oribotic/oribotic-instruments/oribotic-instrument-atmega32u4/src/MPR121/MPR121.cpp

/*******************************************************************************

 Bare Conductive MPR121 library
 ------------------------------

 MPR121.cpp - MPR121 class implementation file

 Based on code by Jim Lindblom and plenty of inspiration from the Freescale
 Semiconductor datasheets and application notes.

 Bare Conductive code written by Stefan Dzisiewski-Smith, Peter Krige
 and Szymon Kaliski.

 This work is licensed under a MIT license https://opensource.org/licenses/MIT

 Copyright (c) 2016, Bare Conductive

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
*******************************************************************************/

extern "C" {
  #include <stdlib.h>
  #include <string.h>
  #include <inttypes.h>
}

#include "MPR121.h"
#include <Arduino.h>

#ifdef ARDUINO_ARCH_AVR
  #include <EEPROM.h>
#endif

#define NOT_INITED_BIT 0
#define ADDRESS_UNKNOWN_BIT 1
#define READBACK_FAIL_BIT 2
#define OVERCURRENT_FLAG_BIT 3
#define OUT_OF_RANGE_BIT 4

MPR121_t::MPR121_t(){
  address = 0x5C;    // default address is 0x5C, for use with Bare Conductive Touch Board
  ECR_backup = 0x00;
  running = false;
  error = 1<<NOT_INITED_BIT; // initially, we're not initialised
  touchData = 0;
  lastTouchData = 0;
  autoTouchStatusFlag = false;
}

void MPR121_t::setRegister(uint8_t reg, uint8_t value){

  bool wasRunning = false;;

  if(reg==MPR121_ECR){  // if we are modding MPR121_ECR, update our internal running status
    if(value&0x3F){
      running = true;
    } else {
      running = false;
    }
  } else if(reg<MPR121_CTL0){
    wasRunning = running;
    if(wasRunning) stop();  // we should ALWAYS be in stop mode for this
                // unless modding MPR121_ECR or GPIO / LED register
  }

    Wire.beginTransmission(address);
    Wire.write(reg);
    Wire.write(value);
    if(Wire.endTransmission()!=0){
      error |= 1<<ADDRESS_UNKNOWN_BIT; // set address unknown bit
    } else {
      error &= ~(1<<ADDRESS_UNKNOWN_BIT);
    }

    if(wasRunning) run();   // restore run mode if necessary
}

uint8_t MPR121_t::getRegister(uint8_t reg){
  uint8_t scratch;

    Wire.beginTransmission(address);
    Wire.write(reg); // set address to read from our requested register
    Wire.endTransmission(false); // repeated start

    if(Wire.requestFrom(address,(uint8_t)1) == 1){  // just a single byte
      error &= ~(1<<ADDRESS_UNKNOWN_BIT); // all good, clear the bit
      scratch = Wire.read();
    } else {
      error |= 1<<ADDRESS_UNKNOWN_BIT; //set the bit - something went wrong
    }

    // auto update errors for registers with error data
    if(reg == MPR121_TS2 && ((scratch&0x80)!=0)){
      error |= 1<<OVERCURRENT_FLAG_BIT;
    } else {
      error &= ~(1<<OVERCURRENT_FLAG_BIT);
    }
    if((reg == MPR121_OORS1 || reg == MPR121_OORS2) && (scratch!=0)){
      error |= 1<<OUT_OF_RANGE_BIT;
    } else {
      error &= ~(1<<OUT_OF_RANGE_BIT);
    }
    return scratch;
}

bool MPR121_t::begin(uint8_t address, uint8_t touchThreshold, uint8_t releaseThreshold, uint8_t interruptPin){

  // SDA and SCL should idle high, but MPR121 can get stuck waiting to complete a transaction
  // this code detects this state and releases us from it

  boolean stuck_transaction = false;
  uint8_t stuck_transaction_retry_count = 0;
  const uint8_t stuck_transaction_retry_MAX = 10;

  ::pinMode( PIN_WIRE_SDA, INPUT_PULLUP );
  ::pinMode( PIN_WIRE_SCL, INPUT_PULLUP );

  do{
    if(( ::digitalRead( PIN_WIRE_SDA ) == LOW ) && ( ::digitalRead( PIN_WIRE_SCL ) == HIGH )){
      stuck_transaction = true;
      ::pinMode( PIN_WIRE_SCL, OUTPUT );
      ::digitalWrite( PIN_WIRE_SCL, LOW );
      delay( 1 ); // this is way longer than required (would be 1.25us at 400kHz) but err on side of caution
      ::pinMode( PIN_WIRE_SCL, INPUT_PULLUP );
      stuck_transaction_retry_count++;
    } else {
      stuck_transaction = false;
    }
  } while ( stuck_transaction && ( stuck_transaction_retry_count < stuck_transaction_retry_MAX ));

  // TODO: add new error code that can be handled externally
  if( stuck_transaction_retry_count > 0){
    if( stuck_transaction ){
    } else {
    }
  }

  // now we've released (if necessary) we can get on with things
  Wire.begin();

  // addresses only valid 0x5A to 0x5D - if we don't change the address it stays at default
  if(address>=0x5A && address<=0x5D)
  {
    this->address = address; // need to be specific here
  }

  error &= ~(1<<NOT_INITED_BIT); // clear NOT_INITED error flag

  if( reset() ){
    // default values...
    applySettings( &defaultSettings );

    // only apply thresholds if they differ from existing defaults
    if( touchThreshold != defaultSettings.TTHRESH ){
      setTouchThreshold( touchThreshold );
    }

    if( releaseThreshold != defaultSettings.RTHRESH ){
      setReleaseThreshold( releaseThreshold );
    }

    if( interruptPin != defaultSettings.INTERRUPT ){
      setInterruptPin( interruptPin );
    }

    return true;

  } else {
    return false;
  }
}

void MPR121_t::clearSavedThresholds() {
  #ifdef ARDUINO_ARCH_AVR
    uint8_t maxElectrodes = 12;
    int len = E2END;

    for(uint8_t i=0; i<13; i++){
      EEPROM.write(len - (i + 1), 255);
      EEPROM.write(len - (i + 1) - maxElectrodes, 255);
    }
  #endif
}

void MPR121_t::restoreSavedThresholds() {
  #ifdef ARDUINO_ARCH_AVR
    uint8_t maxElectrodes = 12;
    int len = E2END;

    for(uint8_t i=0; i<13; i++){
      uint8_t releaseThreshold = EEPROM.read(len - (i + 1));
      uint8_t touchThreshold = EEPROM.read(len - (i + 1) - maxElectrodes);

      if (touchThreshold < 255) {
        setTouchThreshold(i, touchThreshold + 1); // EEPROM values are saved off-by-one
      }
      else {
        setTouchThreshold(i, defaultSettings.TTHRESH);
      }

      if (releaseThreshold < 255) {
        setReleaseThreshold(i, releaseThreshold + 1); // EEPROM values are saved off-by-one
      }
      else {
        setReleaseThreshold(i, defaultSettings.RTHRESH);
      }
    }
  #endif
}

void MPR121_t::goSlow(){
  Wire.setClock(100000L); // set I2C clock to 100kHz
}

void MPR121_t::goFast(){
    Wire.setClock(400000L); // set I2C clock to 400kHz
}

void MPR121_t::run(){
  if(!isInited()) return;
  setRegister(MPR121_ECR, ECR_backup); // restore backup to return to run mode
}

void MPR121_t::stop(){
  if(!isInited()) return;
  ECR_backup = getRegister(MPR121_ECR); // backup MPR121_ECR to restore when we enter run
  setRegister(MPR121_ECR, ECR_backup & 0xC0); // turn off all electrodes to stop
}

bool MPR121_t::reset(){
  // return true if we successfully reset a device at the
  // address we are expecting

  // MPR121_AFE2 is one of the few registers that defaults to a non-zero value -
  // checking it is sensible as reading back an incorrect value implies
  // something went wrong - we also check MPR121_TS2 bit 7 to see if we have an
  // overcurrent flag set

  setRegister(MPR121_SRST, 0x63); // soft reset

  if(getRegister(MPR121_AFE2)!=0x24){
    error |= 1<<READBACK_FAIL_BIT;
  } else {
    error &= ~(1<<READBACK_FAIL_BIT);
  }

  if((getRegister(MPR121_TS2)&0x80)!=0){
    error |= 1<<OVERCURRENT_FLAG_BIT;
  } else {
    error &= ~(1<<OVERCURRENT_FLAG_BIT);
  }

  if(getError()==NOT_INITED || getError()==NO_ERROR){ // if our only error is that we are not inited...
    return true;
  } else {
    return false;
  }
}

void MPR121_t::applySettings(MPR121_settings_t *settings){
  bool wasRunning = running;
  if(wasRunning) stop();  // can't change most regs when running - checking
              // here avoids multiple stop() / run() calls

  setRegister(MPR121_MHDR,settings->MHDR);
  setRegister(MPR121_NHDR,settings->NHDR);
  setRegister(MPR121_NCLR,settings->NCLR);
  setRegister(MPR121_FDLR,settings->FDLR);
  setRegister(MPR121_MHDF,settings->MHDF);
  setRegister(MPR121_NHDF,settings->NHDF);
  setRegister(MPR121_NCLF,settings->NCLF);
  setRegister(MPR121_FDLF,settings->FDLF);
  setRegister(MPR121_NHDT,settings->NHDT);
  setRegister(MPR121_NCLT,settings->NCLT);
  setRegister(MPR121_FDLT,settings->FDLT);
  setRegister(MPR121_MHDPROXR,settings->MHDPROXR);
  setRegister(MPR121_NHDPROXR,settings->NHDPROXR);
  setRegister(MPR121_NCLPROXR,settings->NCLPROXR);
  setRegister(MPR121_FDLPROXR,settings->FDLPROXR);
  setRegister(MPR121_MHDPROXF,settings->MHDPROXF);
  setRegister(MPR121_NHDPROXF,settings->NHDPROXF);
  setRegister(MPR121_NCLPROXF,settings->NCLPROXF);
  setRegister(MPR121_FDLPROXF,settings->FDLPROXF);
  setRegister(MPR121_NHDPROXT,settings->NHDPROXT);
  setRegister(MPR121_NCLPROXT,settings->NCLPROXT);
  setRegister(MPR121_FDLPROXT,settings->FDLPROXT);
  setRegister(MPR121_DTR, settings->DTR);
  setRegister(MPR121_AFE1, settings->AFE1);
  setRegister(MPR121_AFE2, settings->AFE2);
  setRegister(MPR121_ACCR0, settings->ACCR0);
  setRegister(MPR121_ACCR1, settings->ACCR1);
  setRegister(MPR121_USL, settings->USL);
  setRegister(MPR121_LSL, settings->LSL);
  setRegister(MPR121_TL, settings->TL);

  setRegister(MPR121_ECR, settings->ECR);

  error &= ~(1<<NOT_INITED_BIT); // clear not inited error as we have just inited!
  setTouchThreshold(settings->TTHRESH);
  setReleaseThreshold(settings->RTHRESH);
  setInterruptPin(settings->INTERRUPT);

  if(wasRunning) run();
}

mpr121_error_t MPR121_t::getError(){

  // important - this resets the IRQ pin - as does any I2C comms

  getRegister(MPR121_OORS1);  // OOR registers - we may not have read them yet,
  getRegister(MPR121_OORS2);  // whereas the other errors should have been caught

  // order of error precedence is determined in this logic block

  if(!isInited()) return NOT_INITED; // this has its own checker function

  if((error & (1<<ADDRESS_UNKNOWN_BIT)) != 0){
    return ADDRESS_UNKNOWN;
  } else if((error & (1<<READBACK_FAIL_BIT)) != 0){
    return READBACK_FAIL;
  } else if((error & (1<<OVERCURRENT_FLAG_BIT)) != 0){
    return OVERCURRENT_FLAG;
  } else if((error & (1<<OUT_OF_RANGE_BIT)) != 0){
    return OUT_OF_RANGE;
  } else return NO_ERROR;

}

void MPR121_t::clearError(){
  error = 0;
}

bool MPR121_t::isRunning(){
  return running;
}

bool MPR121_t::isInited(){
  return (error & (1<<NOT_INITED_BIT)) == 0;
}

void MPR121_t::updateTouchData(){
  if(!isInited()) return;

  autoTouchStatusFlag = false;

  lastTouchData = touchData;
  touchData = (unsigned int)getRegister(MPR121_TS1) + ((unsigned int)getRegister(MPR121_TS2)<<8);
}

bool MPR121_t::getTouchData(uint8_t electrode){
  if(electrode>12 || !isInited()) return false; // avoid out of bounds behaviour

  return((touchData>>electrode)&1);
}

uint8_t MPR121_t::getNumTouches(){
  if(!isInited()) return(0xFF);

  uint8_t scratch = 0;
  for(uint8_t i=0; i<13; i++){
    if(getTouchData(i)) scratch++;
  }

  return(scratch);
}

bool MPR121_t::getLastTouchData(uint8_t electrode){
  if(electrode>12 || !isInited()) return false; // avoid out of bounds behaviour

  return((lastTouchData>>electrode)&1);
}

bool MPR121_t::updateFilteredData(){
  if(!isInited()) return(false);

  uint8_t LSB, MSB;

  Wire.beginTransmission(address);
  Wire.write(MPR121_E0FDL); // set address register to read from the start of the
                //filtered data
  Wire.endTransmission(false); // repeated start

  if(touchStatusChanged()) {
    autoTouchStatusFlag = true;
  }

  if(Wire.requestFrom(address,(uint8_t)26)==26){
    for(int i=0; i<13; i++){ // 13 filtered values
      if(touchStatusChanged()) {
        autoTouchStatusFlag = true;
      }
      LSB = Wire.read();
      if(touchStatusChanged()) {
        autoTouchStatusFlag = true;
      }
      MSB = Wire.read();
      filteredData[i] = ((MSB << 8) | LSB);
    }
    return(true);
  } else {
    // if we don't get back all 26 values we requested, don't update the FDAT values
    // and return false
    return(false);
  }
}

int MPR121_t::getFilteredData(uint8_t electrode){
  if(electrode>12 || !isInited()) return(0xFFFF); // avoid out of bounds behaviour

  return(filteredData[electrode]);
}

bool MPR121_t::updateBaselineData(){
  if(!isInited()) return(false);

  Wire.beginTransmission(address);
  Wire.write(MPR121_E0BV);  // set address register to read from the start of the
                // baseline data
  Wire.endTransmission(false); // repeated start

  if(touchStatusChanged()) {
    autoTouchStatusFlag = true;
  }

  if(Wire.requestFrom(address,(uint8_t)13)==13){
    for(int i=0; i<13; i++){ // 13 filtered values
      if(touchStatusChanged()) {
        autoTouchStatusFlag = true;
      }
      baselineData[i] = Wire.read()<<2;
    }
    return(true);
    } else {
      // if we don't get back all 26 values we requested, don't update the BVAL values
      // and return false
    return(false);
  }
}

int MPR121_t::getBaselineData(uint8_t electrode){
  if(electrode>12 || !isInited()) return(0xFFFF); // avoid out of bounds behaviour

  return(baselineData[electrode]);
}

bool MPR121_t::isNewTouch(uint8_t electrode){
  if(electrode>12 || !isInited()) return(false); // avoid out of bounds behaviour
  return((getLastTouchData(electrode) == false) && (getTouchData(electrode) == true));
}

bool MPR121_t::isNewRelease(uint8_t electrode){
  if(electrode>12 || !isInited()) return(false); // avoid out of bounds behaviour
  return((getLastTouchData(electrode) == true) && (getTouchData(electrode) == false));
}

void MPR121_t::updateAll(){
  updateTouchData();
  updateBaselineData();
  updateFilteredData();
}

void MPR121_t::setTouchThreshold(uint8_t val){
  if(!isInited()) return;
  bool wasRunning = running;

  if(wasRunning) stop();  // can only change thresholds when not running
              // checking here avoids multiple stop() / run()
              // calls

  for(uint8_t i=0; i<13; i++){
    setTouchThreshold(i, val);
  }

  if(wasRunning) run();
}

void MPR121_t::saveTouchThreshold(uint8_t electrode, uint8_t val){
  #ifdef ARDUINO_ARCH_AVR
    if(electrode>12 || !isInited()) return; // avoid out of bounds behaviour

    setTouchThreshold(electrode, val);

    // store to EEPROM
    uint8_t maxElectrodes = 12;
    int len = E2END;
    int addr = len - maxElectrodes - (electrode + 1);
    EEPROM.write(addr, val - 1); // val - 1 so 255 stays as never-written-to
  #endif
}

void MPR121_t::setTouchThreshold(uint8_t electrode, uint8_t val){
  if(electrode>12 || !isInited()) return; // avoid out of bounds behaviour

  // this relies on the internal register map of the MPR121
  setRegister(MPR121_E0TTH + (electrode<<1), val);
}

void MPR121_t::setReleaseThreshold(uint8_t val){
  if(!isInited()) return;
  bool wasRunning = running;

  if(wasRunning) stop();  // can only change thresholds when not running
              // checking here avoids multiple stop / starts

  for(uint8_t i=0; i<13; i++){
    setReleaseThreshold(i,val);
  }

  if(wasRunning) run();
}

void MPR121_t::setReleaseThreshold(uint8_t electrode, uint8_t val){
  if(electrode>12 || !isInited()) return; // avoid out of bounds behaviour

  // this relies on the internal register map of the MPR121
  setRegister(MPR121_E0RTH + (electrode<<1), val);
}

void MPR121_t::saveReleaseThreshold(uint8_t electrode, uint8_t val){
  #ifdef ARDUINO_ARCH_AVR
    if(electrode>12 || !isInited()) return; // avoid out of bounds behaviour

    setReleaseThreshold(electrode, val);

    // store to EEPROM
    int len = E2END;
    int addr = len - (electrode + 1);
    EEPROM.write(addr, val - 1); // val - 1 so 255 stays as never-written-to
  #endif
}

uint8_t MPR121_t::getTouchThreshold(uint8_t electrode){
  if(electrode>12 || !isInited()) return(0xFF); // avoid out of bounds behaviour
  return(getRegister(MPR121_E0TTH+(electrode<<1))); // "255" issue is in here somewhere
  //return(101);
}

uint8_t MPR121_t::getReleaseThreshold(uint8_t electrode){
  if(electrode>12 || !isInited()) return(0xFF); // avoid out of bounds behaviour
  return(getRegister(MPR121_E0RTH+(electrode<<1))); // "255" issue is in here somewhere
  //return(51);
}

void MPR121_t::setInterruptPin(uint8_t pin){
  // :: here forces the compiler to use Arduino's pinMode, not MPR121's
  if(!isInited()) return;
  ::pinMode(pin, INPUT_PULLUP);
  interruptPin = pin;
}

bool MPR121_t::touchStatusChanged(){
  // :: here forces the compiler to use Arduino's digitalRead, not MPR121's
  return(autoTouchStatusFlag || (!::digitalRead(interruptPin)));
}

void MPR121_t::setProxMode(mpr121_proxmode_t mode){

  if(!isInited()) return;

  bool wasRunning = running;

  if(wasRunning) stop();

  switch(mode){
    case PROX_DISABLED:
      ECR_backup &= ~(3<<4);  // ELEPROX_EN[1:0] = 00
      break;
    case PROX_0_1:
      ECR_backup |=  (1<<4);  // ELEPROX_EN[1:0] = 01
      ECR_backup &= ~(1<<5);
      break;
    case PROX_0_3:
      ECR_backup &= ~(1<<4);  // ELEPROX_EN[1:0] = 10
      ECR_backup |=  (1<<5);
      break;
    case PROX_0_11:
      ECR_backup |=  (3<<4);  // ELEPROX_EN[1:0] = 11
      break;
  }

  if(wasRunning) run();
}

void MPR121_t::setCalibrationLock(mpr121_cal_lock_t lock){

  if(!isInited()) return;

  bool wasRunning = running;

  if(wasRunning) stop();

  switch(lock){
    case CAL_LOCK_ENABLED:
      ECR_backup &= ~(3<<6);  // CL[1:0] = 00
      break;
    case CAL_LOCK_DISABLED:
      ECR_backup |=  (1<<6);  // CL[1:0] = 01
      ECR_backup &= ~(1<<7);
      break;
    case CAL_LOCK_ENABLED_5_BIT_COPY:
      ECR_backup &= ~(1<<6);  // CL[1:0] = 10
      ECR_backup |=  (1<<7);
      break;
    case CAL_LOCK_ENABLED_10_BIT_COPY:
      ECR_backup |=  (3<<4);  // CL[1:0] = 11
      break;
  }

  if(wasRunning) run();
}

void MPR121_t::setGlobalCDC(uint8_t CDC){
  if(CDC > 63) return; // current is only valid 0..63uA

  setRegister(MPR121_AFE1, (getRegister(MPR121_AFE1) & 0xC0) | CDC);
}

void MPR121_t::setElectrodeCDC(uint8_t electrode, uint8_t CDC){
  if(CDC > 63 || electrode > 12) return; // current is only valid 0..63uA, electrode only valid 0..12

  setRegister(MPR121_CDC0 + electrode, CDC);
}

void MPR121_t::setGlobalCDT(mpr121_CDT_t CDT){
  setRegister(MPR121_AFE2, (getRegister(MPR121_AFE2) & 0x1F) | (CDT << 5));
}

void MPR121_t::setElectrodeCDT(uint8_t electrode, mpr121_CDT_t CDT){
  setRegister(MPR121_CDT01 + (electrode >> 1), (getRegister(MPR121_CDT01 + (electrode >> 1)) & (0x0F << (((electrode + 1) % 2)<<2))) | (CDT << ((electrode % 2)<<2)));
}

bool MPR121_t::autoSetElectrodeCDC(uint8_t electrode, uint16_t VCC_mV){
  uint16_t upper_limit_FDAT = (uint16_t)((((uint32_t)VCC_mV - 700)*256)/VCC_mV) << 2;
  uint16_t target_FDAT = (uint16_t)(((uint32_t)upper_limit_FDAT * 90) / 100);
  uint16_t lower_limit_FDAT = (uint16_t)(((uint32_t)upper_limit_FDAT * 65) / 100);

  uint16_t this_value;
  int16_t last_distance;
  int16_t this_distance;

  const uint8_t max_num_delay_loops = 100;
  uint8_t num_delay_loops;

  bool scratch = false; // default to failure
  uint8_t saved_num_enabled_electrodes = getNumEnabledElectrodes();

  setNumEnabledElectrodes(electrode + 1); // reducing the number of running electrodes to a minimum speeds things up
  if(!running) run();

  for(uint8_t CDC = 1; CDC < 63; CDC ++){
    setElectrodeCDC(electrode, CDC);
    num_delay_loops = 0;

    do{
      updateFilteredData();
    } while((getFilteredData(electrode) == 0) && (num_delay_loops++ < max_num_delay_loops));

    this_value = getFilteredData(electrode);

    this_distance = (uint16_t)(abs((int16_t)this_value - (int16_t)target_FDAT)); // TODO: tidy up signed / unsigned types here
    if(CDC > 1){ // only need to see if we need to quit once we have at least two measurements to compare
      if(this_distance > last_distance){ // if we got further away from our target this setting should work (slightly prefer higher values)
        setElectrodeCDC(electrode, CDC);
        if((this_value >= lower_limit_FDAT) && (this_value <= upper_limit_FDAT)){
          scratch = true; // success
        }
        break;
      } else if(CDC == 63){ // or if we're at the end of the available adjustment, see if we're close enough
        setElectrodeCDC(electrode, CDC);
        if((this_value >= lower_limit_FDAT) && (this_value <= upper_limit_FDAT)){
          scratch = true; // success
        }
        break;
      }
    }
    last_distance = this_distance;
  }

  setRegister(MPR121_ECR, ECR_backup);
  setNumEnabledElectrodes(saved_num_enabled_electrodes); // have to do this separately as ECR_backup gets invalidated by setNumEnabledElectrodes(electrode + 1);

  return(scratch);
}

bool MPR121_t::autoSetElectrodeCDC(uint8_t electrode){
  // default to 3.3V VCC if not explicitly stated
  return(autoSetElectrodeCDC(electrode, 3300));
}

bool MPR121_t::autoSetElectrodeCDC(){
  bool scratch = true;
  for(uint8_t i=0; i<getNumEnabledElectrodes(); i++){
    scratch = autoSetElectrodeCDC(i) ? scratch : false;
  }

  return(scratch);
}

bool MPR121_t::autoSetElectrodes(uint16_t VCC_mV, bool fixedChargeTime){
  uint8_t USL = (uint8_t)((((uint32_t)VCC_mV - 700)*256)/VCC_mV);
  uint8_t T_L = (uint8_t)(((uint16_t)USL * 90) / 100);
  uint8_t LSL = (uint8_t)(((uint16_t)USL * 65) / 100);
  bool wasRunning = running;

  stop();

  setRegister(MPR121_USL, USL);
  setRegister(MPR121_TL, T_L);
  setRegister(MPR121_LSL, LSL);

  // don't enable retry, copy other settings from elsewhere
  // setRegister(MPR121_ACCR0, 1 | ((ECR_backup & 0xC0) >> 4) | (getRegister(MPR121_AFE1) & 0xC0));
  // enable retry, copy other settings from elsewhere
  setRegister(MPR121_ACCR0, 0x31 | ((ECR_backup & 0xC0) >> 4) | (getRegister(MPR121_AFE1) & 0xC0)); 
  // fixed charge time is useful for designs with higher lead-in resistance - e.g. using Bare Electric Paint
  setRegister(MPR121_ACCR1, fixedChargeTime ? 1 << 7 : 0); 

  if(wasRunning){
    run();
  }

  // wait a bit before reading back the out or range register
  delayMicroseconds(10);

  return(!(getRegister(MPR121_OORS2) & 0xC0));
}

bool MPR121_t::autoSetElectrodes(bool fixedChargeTime){
  return(autoSetElectrodes(3300, fixedChargeTime));
}

void MPR121_t::setNumDigPins(uint8_t numPins){
  if(!isInited()) return;
  bool wasRunning = running;

  if(numPins>8) numPins = 8; // maximum number of GPIO pins is 8 out of 12

  if(wasRunning){
    stop(); // have to stop to change MPR121_ECR
  }
  ECR_backup = (0x0F&(12-numPins)) | (ECR_backup&0xF0);
  if(wasRunning){
    run();
  }
}

void MPR121_t::setNumEnabledElectrodes(uint8_t numElectrodes){
  if(!isInited()) return;
  bool wasRunning = running;

  if(numElectrodes>12) numElectrodes = 12; // avoid out-of-bounds behaviour

  if(wasRunning){
    stop(); // have to stop to change MPR121_ECR
  }
  ECR_backup = (0x0F&numElectrodes) | (ECR_backup&0xF0);
  if(wasRunning){
    run();
  }
}

uint8_t MPR121_t::getNumEnabledElectrodes(){
  if(!isInited()) return(0xFF);

  return(getRegister(MPR121_ECR) & 0x0F);
}

void MPR121_t::pinMode(uint8_t electrode, mpr121_pinf_t mode){

  // only valid for ELE4..ELE11
  if(electrode<4 || electrode >11 || !isInited()) return;

  // LED0..LED7
  uint8_t bitmask = 1<<(electrode-4);

  switch(mode){
    case INPUT_PULLDOWN:
      // MPR121_EN = 1
      // MPR121_DIR = 0
      // MPR121_CTL0 = 1
      // MPR121_CTL1 = 0
      setRegister(MPR121_EN, getRegister(MPR121_EN) | bitmask);
      setRegister(MPR121_DIR, getRegister(MPR121_DIR) & ~bitmask);
      setRegister(MPR121_CTL0, getRegister(MPR121_CTL0) | bitmask);
      setRegister(MPR121_CTL1, getRegister(MPR121_CTL1) & ~bitmask);
      break;

    case OUTPUT_HIGHSIDE:
      // MPR121_EN = 1
      // MPR121_DIR = 1
      // MPR121_CTL0 = 1
      // MPR121_CTL1 = 1
      setRegister(MPR121_EN, getRegister(MPR121_EN) | bitmask);
      setRegister(MPR121_DIR, getRegister(MPR121_DIR) | bitmask);
      setRegister(MPR121_CTL0, getRegister(MPR121_CTL0) | bitmask);
      setRegister(MPR121_CTL1, getRegister(MPR121_CTL1) | bitmask);
      break;

    case OUTPUT_LOWSIDE:
      // MPR121_EN = 1
      // MPR121_DIR = 1
      // MPR121_CTL0 = 1
      // MPR121_CTL1 = 0
      setRegister(MPR121_EN, getRegister(MPR121_EN) | bitmask);
      setRegister(MPR121_DIR, getRegister(MPR121_DIR) | bitmask);
      setRegister(MPR121_CTL0, getRegister(MPR121_CTL0) | bitmask);
      setRegister(MPR121_CTL1, getRegister(MPR121_CTL1) & ~bitmask);
      break;

    default:
      break;
  }
}

void MPR121_t::pinMode(uint8_t electrode, int mode){
  // this is to catch the fact that Arduino prefers its definitions of
  // INPUT, OUTPUT and INPUT_PULLUP to ours...

  // only valid for ELE4..ELE11
  if(electrode<4 || electrode >11 || !isInited()) return;

  uint8_t bitmask = 1<<(electrode-4);

  switch(mode){
    case OUTPUT:
      // MPR121_EN = 1
      // MPR121_DIR = 1
      // MPR121_CTL0 = 0
      // MPR121_CTL1 = 0
      setRegister(MPR121_EN, getRegister(MPR121_EN) | bitmask);
      setRegister(MPR121_DIR, getRegister(MPR121_DIR) | bitmask);
      setRegister(MPR121_CTL0, getRegister(MPR121_CTL0) & ~bitmask);
      setRegister(MPR121_CTL1, getRegister(MPR121_CTL1) & ~bitmask);
      break;

    case INPUT:
      // MPR121_EN = 1
      // MPR121_DIR = 0
      // MPR121_CTL0 = 0
      // MPR121_CTL1 = 0
      setRegister(MPR121_EN, getRegister(MPR121_EN) | bitmask);
      setRegister(MPR121_DIR, getRegister(MPR121_DIR) & ~bitmask);
      setRegister(MPR121_CTL0, getRegister(MPR121_CTL0) & ~bitmask);
      setRegister(MPR121_CTL1, getRegister(MPR121_CTL1) & ~bitmask);
      break;

    case INPUT_PULLUP:
      // MPR121_EN = 1
      // MPR121_DIR = 0
      // MPR121_CTL0 = 1
      // MPR121_CTL1 = 1
      setRegister(MPR121_EN, getRegister(MPR121_EN) | bitmask);
      setRegister(MPR121_DIR, getRegister(MPR121_DIR) & ~bitmask);
      setRegister(MPR121_CTL0, getRegister(MPR121_CTL0) | bitmask);
      setRegister(MPR121_CTL1, getRegister(MPR121_CTL1) | bitmask);
      break;

    default:
      break;
  }
}

void MPR121_t::digitalWrite(uint8_t electrode, uint8_t val){

  // avoid out of bounds behaviour

  if(electrode<4 || electrode>11 || !isInited()) return;

  if(val){
    setRegister(MPR121_SET, 1<<(electrode-4));
  } else {
    setRegister(MPR121_CLR, 1<<(electrode-4));
  }
}

void MPR121_t::digitalToggle(uint8_t electrode){

  // avoid out of bounds behaviour

  if(electrode<4 || electrode>11 || !isInited()) return;

  setRegister(MPR121_TOG, 1<<(electrode-4));
}

bool MPR121_t::digitalRead(uint8_t electrode){

  // avoid out of bounds behaviour

  if(electrode<4 || electrode>11 || !isInited()) return false;

  return(((getRegister(MPR121_DAT)>>(electrode-4))&1)==1);
}

void MPR121_t::analogWrite(uint8_t electrode, uint8_t value){
  // LED output 5 (ELE9) and output 6 (ELE10) have a PWM bug
  // https://community.nxp.com/thread/305474

  // avoid out of bounds behaviour

  if(electrode<4 || electrode>11 || !isInited()) return;

  uint8_t shiftedVal = value>>4;

  if(shiftedVal > 0){
    setRegister(MPR121_SET, 1<<(electrode-4)); // normal PWM operation
  } else {
    // this make a 0 PWM setting turn off the output
    setRegister(MPR121_CLR, 1<<(electrode-4));
  }

  switch(electrode-4){

  case 0:
    setRegister(MPR121_PWM0, (shiftedVal & 0x0F) | (getRegister(MPR121_PWM0) & 0xF0));
    break;
  case 1:
    setRegister(MPR121_PWM0, ((shiftedVal & 0x0F)<<4) | (getRegister(MPR121_PWM0) & 0x0F));
    break;
  case 2:
    setRegister(MPR121_PWM1, (shiftedVal & 0x0F) | (getRegister(MPR121_PWM1) & 0xF0));
    break;
  case 3:
    setRegister(MPR121_PWM1, ((shiftedVal & 0x0F)<<4) | (getRegister(MPR121_PWM1) & 0x0F));
    break;
  case 4:
    setRegister(MPR121_PWM2, (shiftedVal & 0x0F) | (getRegister(MPR121_PWM2) & 0xF0));
    break;
  case 5:
    setRegister(MPR121_PWM2, ((shiftedVal & 0x0F)<<4) | (getRegister(MPR121_PWM2) & 0x0F));
    break;
  case 6:
    setRegister(MPR121_PWM3, (shiftedVal & 0x0F) | (getRegister(MPR121_PWM3) & 0xF0));
    break;
  case 7:
    setRegister(MPR121_PWM3, ((shiftedVal & 0x0F)<<4) | (getRegister(MPR121_PWM3) & 0x0F));
    break;
  }
}

void MPR121_t::setSamplePeriod(mpr121_sample_interval_t period){
  setRegister(MPR121_AFE2, (getRegister(MPR121_AFE2) & 0xF8) | (period & 0x07));
}

void MPR121_t::setFFI(mpr121_FFI_t FFI){
  setRegister(MPR121_AFE1, (getRegister(MPR121_AFE1) & 0x3F) | ((FFI & 0x03) << 6));
}

void MPR121_t::setSFI(mpr121_SFI_t SFI){
  setRegister(MPR121_AFE2, (getRegister(MPR121_AFE2) & 0xE7) | ((SFI & 0x03) << 3));
}

// MPR121_t MPR121_0 = MPR121_t();
// MPR121_t MPR121_1 = MPR121_t();
// MPR121_t MPR121_2 = MPR121_t();
// MPR121_t MPR121_3 = MPR121_t();
