oribotic/oribotic-instruments/oribotic-instrument-atmega32u4/instrument_K48.h

/*
 * Copyright (c) 2023 Matthew Gardiner
 *
 * MIT License.
 * For information on usage and redistribution, and for a DISCLAIMER OF ALL
 * WARRANTIES, see the file, "LICENSE.txt," in this distribution.
 *
 * See https://github.com/oribotic/oribotic-instruments for documentation
 *
 */

// instrument definion for K48 
// Kresling 48 panel instrument

#include "ORICORD.h"

#define SOFT_LOW_OFFSET 25
#define LO_HARD_OFFSET 25
#define PINCOUNT 48
#define MPRCOUNT 4
//#define PANELGROUPS 1

#define CAL_BTN 5 
#define HI_BTN 9
#define LO_BTN 6
#define LED1 13
#define LED2 10
#define LED3 8
#define BTN_COUNT 3
#define PANELCOUNT 48
