oribotic/oribotic-instruments/oribotic-instrument-atmega32u4/music.scales.h

/*
 * Copyright (c) 2023 Matthew Gardiner
 *
 * MIT License.
 * For information on usage and redistribution, and for a DISCLAIMER OF ALL
 * WARRANTIES, see the file, "LICENSE.txt," in this distribution.
 *
 * See https://github.com/oribotic/oribotic-instruments for documentation
 *
 */
#include <Arduino.h>

#ifndef MUSIC_SCALES_H
#define MUSIC_SCALES_H

#define MAXSCALE 8 // max allowed scale index

struct scaleTones
{
  char title[5];
  byte tones;
};

extern uint8_t rootNote;
extern uint8_t scale[8];

extern struct scaleTones availableScales[8];
void generateMidiScale (uint8_t index, uint8_t root);
uint8_t changeScale (uint8_t value); // returns new value if set

#endif // MUSIC_SCALES_H
